jaycee1980/amica-psu/pictures/IMG_4817.JPG

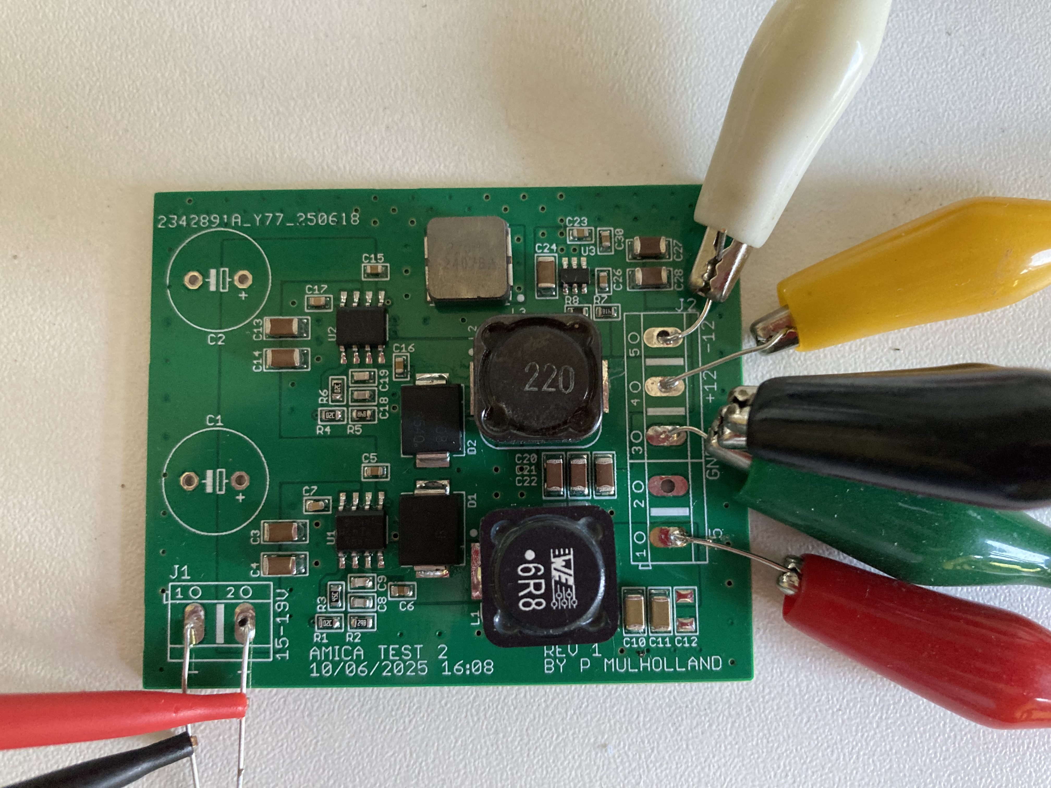
pictures/IMG_4817.JPG
