jaycee1980/amica-psu/pictures/IMG_4818.JPG

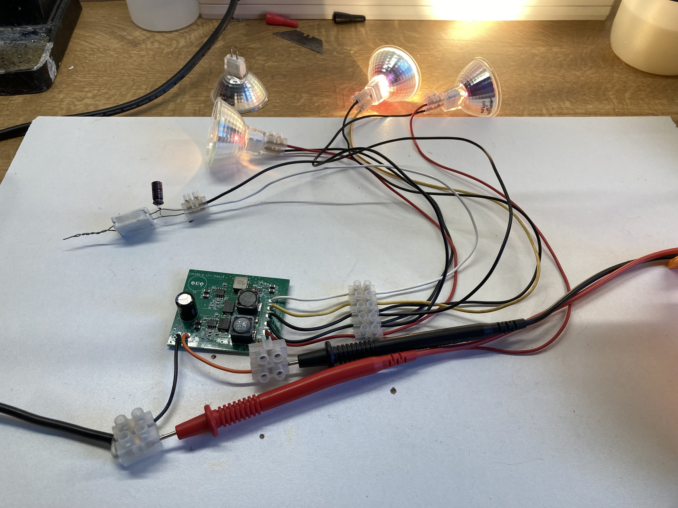
pictures/IMG_4818.JPG
