jaycee1980/amica-psu/pictures/IMG_4845.JPG

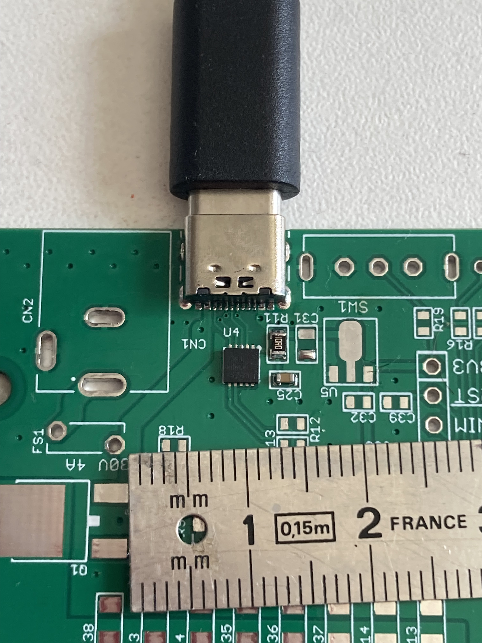
pictures/IMG_4845.JPG
