jaycee1980/amica-psu/pictures/IMG_4875.JPG

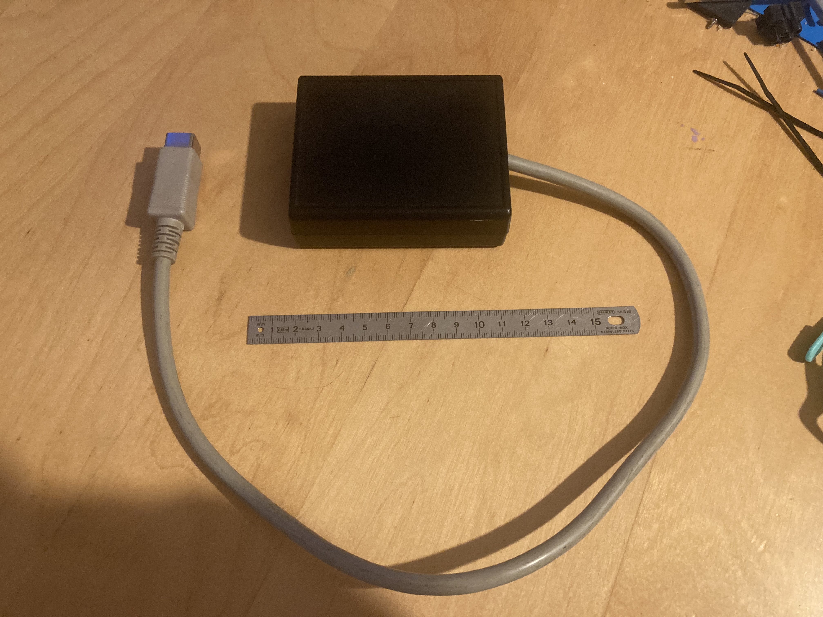
pictures/IMG_4875.JPG
