jaycee1980/amica-psu/pictures/IMG_4881.JPG

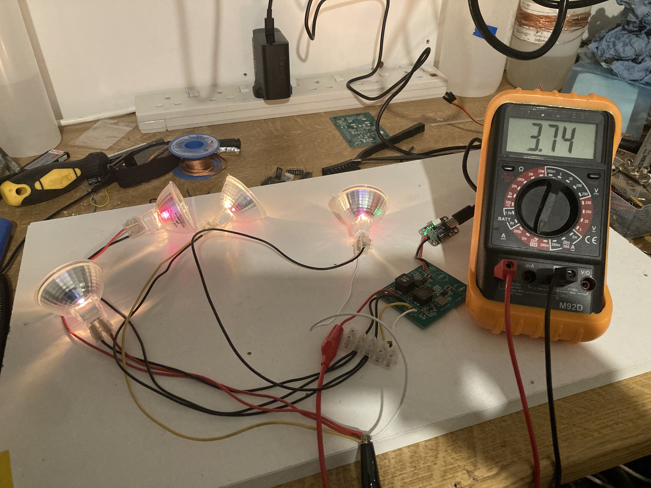
pictures/IMG_4881.JPG
