jaycee1980/amica-psu/pictures/IMG_4923.JPG

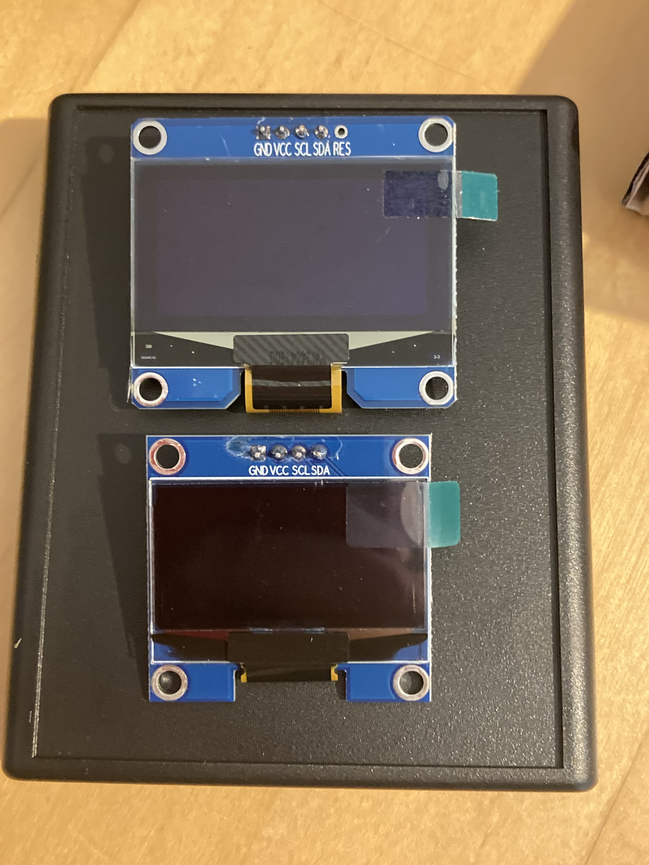
pictures/IMG_4923.JPG
